Vedatori/Time-O-Mat/Mechanics/Box/Box - Front.stl

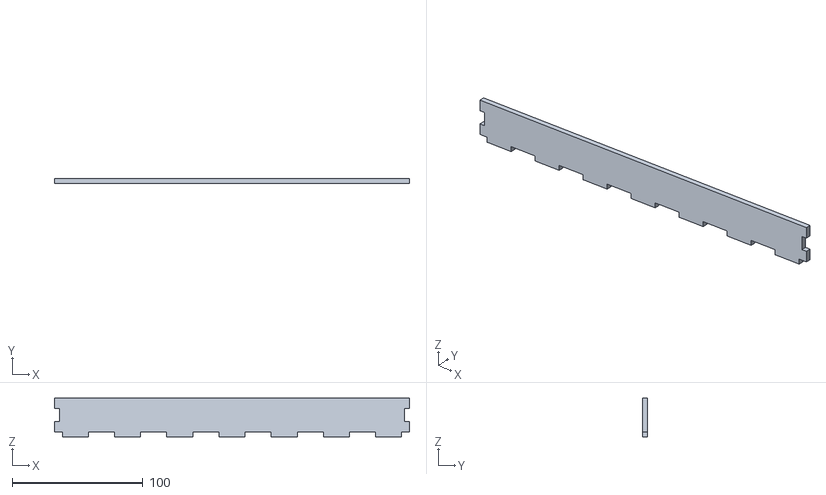
[picture p195: CAD file, 2022-08-20]
Mechanics/Box/Box - Front.stl
272.0 x 3.80 x 29.8
