Vedatori/Time-O-Mat/Mechanics/Eight/Eight v3 - Dot 3DP.stl

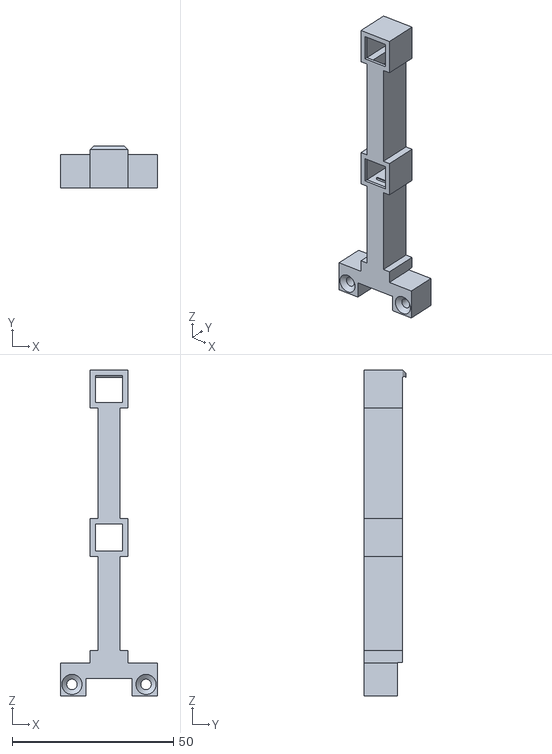
[picture p196: CAD file, 2022-08-20]
Mechanics/Eight/Eight v3 - Dot 3DP.stl
30.0 x 13.0 x 101.2
