Vedatori/Time-O-Mat/Mechanics/Eight/Eight v3 - Diffuser.stl

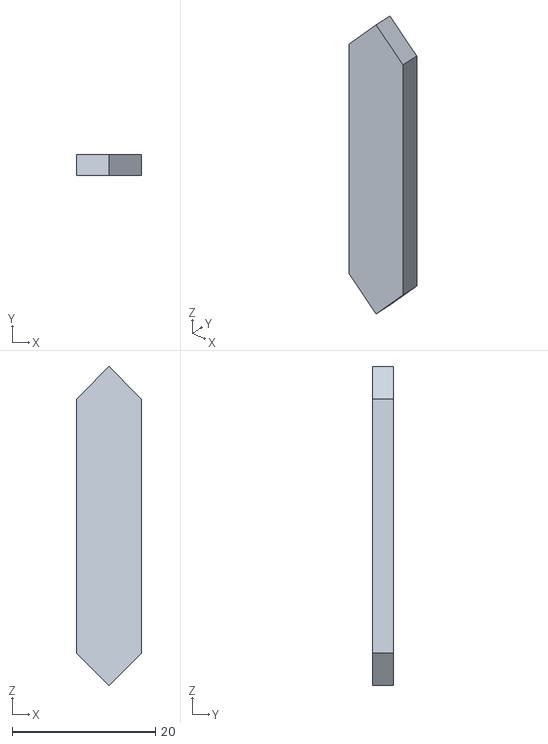
[picture p197: CAD file, 2022-08-20]
Mechanics/Eight/Eight v3 - Diffuser.stl
9.10 x 3.00 x 44.6
