Vedatori/Time-O-Mat/Mechanics/Box/Box - Stand 3DP.stl

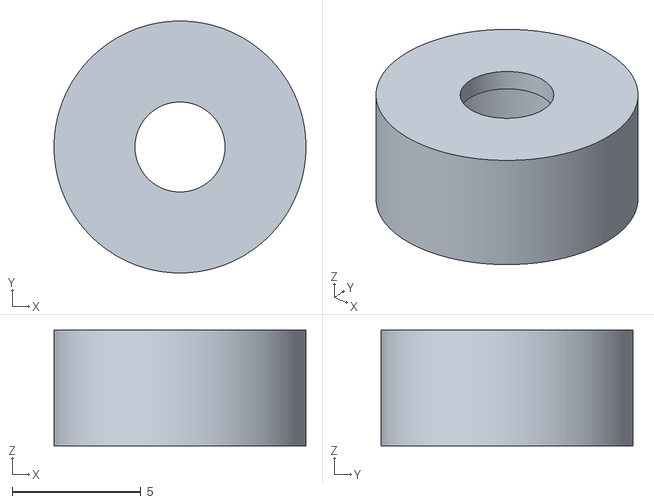
[picture p198: CAD file, 2022-08-20]
Mechanics/Box/Box - Stand 3DP.stl
9.80 x 9.80 x 4.50
