Vedatori/Time-O-Mat/Mechanics/Eight/Eight v3 - Dot spacer 3DP.stl

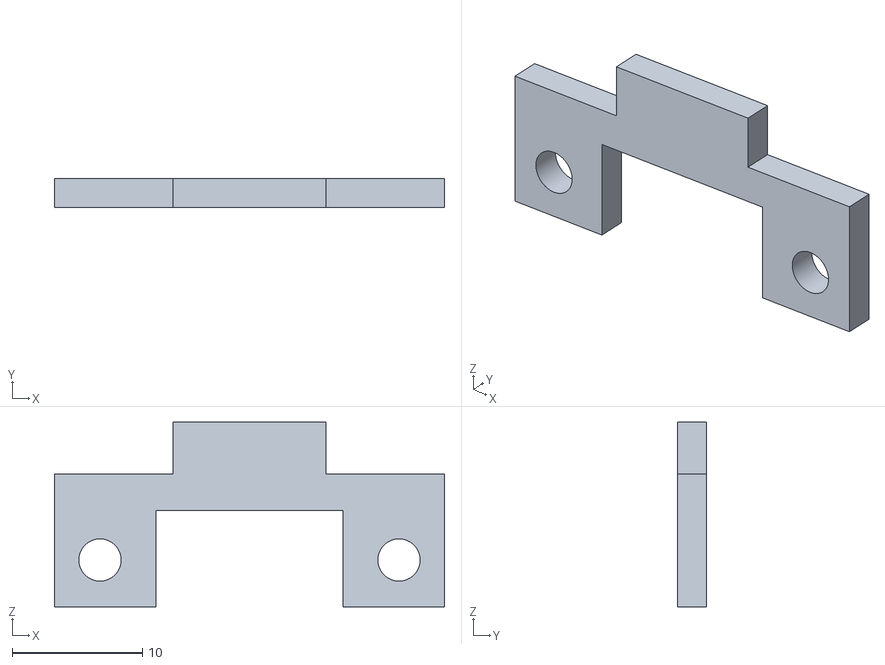
[picture p199: CAD file, 2022-08-20]
Mechanics/Eight/Eight v3 - Dot spacer 3DP.stl
30.0 x 2.25 x 14.2
