Vedatori/Time-O-Mat/Mechanics/Box/Box - Holder pt2 3DP.stl

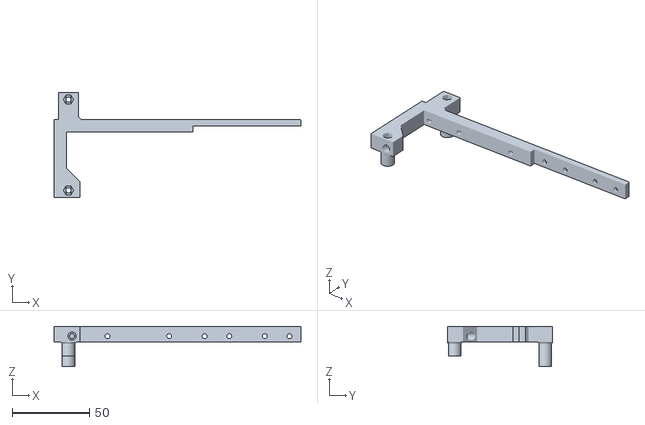
[picture p200: CAD file, 2022-08-20]
Mechanics/Box/Box - Holder pt2 3DP.stl
160.2 x 68.0 x 26.0
