Vedatori/Time-O-Mat/Mechanics/Box/box.dxf

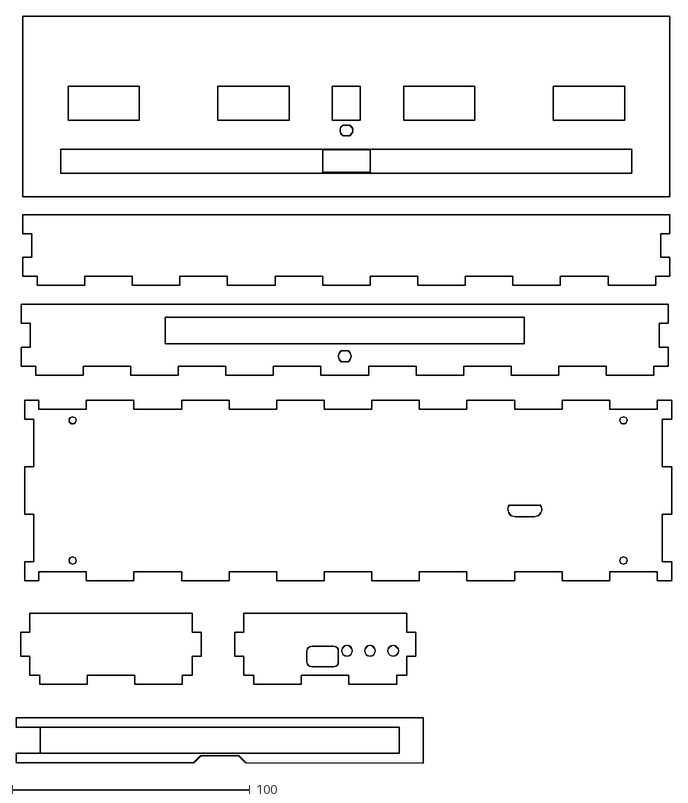
[picture p201: CAD file, 2022-08-20]
Mechanics/Box/box.dxf
275.4 x 314.1
