Vedatori/Time-O-Mat/Mechanics/Box/Box - Right.stl

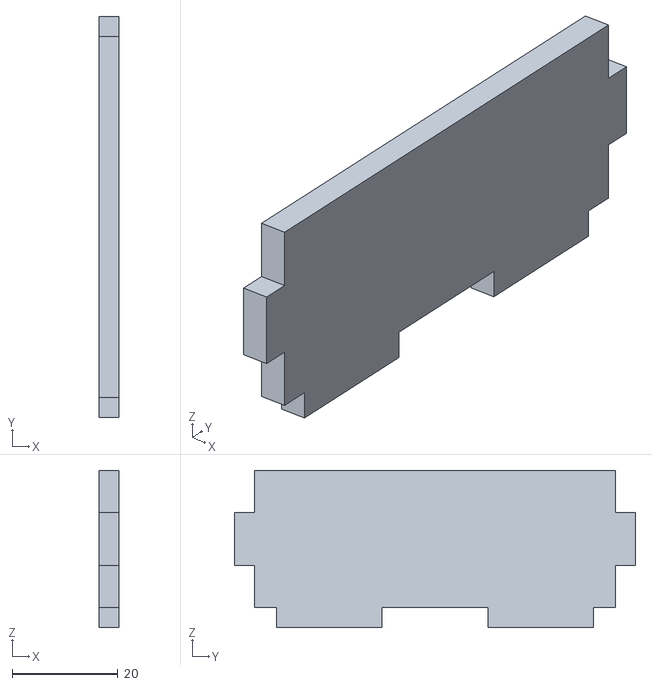
[picture p202: CAD file, 2022-08-20]
Mechanics/Box/Box - Right.stl
3.80 x 76.0 x 29.8
