Vedatori/Time-O-Mat/Mechanics/Box/Box - Holder pt1 3DP.stl

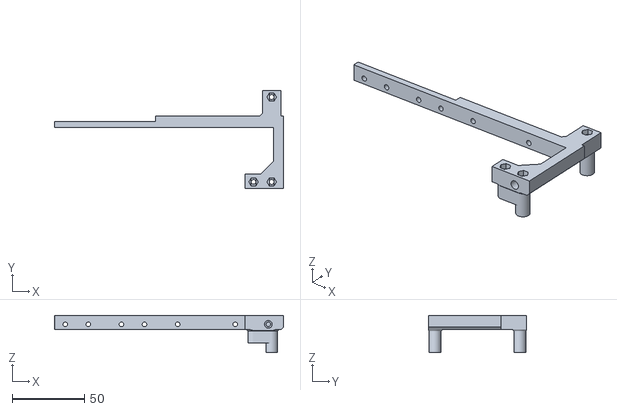
[picture p203: CAD file, 2022-08-20]
Mechanics/Box/Box - Holder pt1 3DP.stl
159.0 x 68.0 x 26.0
