Vedatori/Time-O-Mat/Mechanics/Box/Box - LED strip bracket.stl

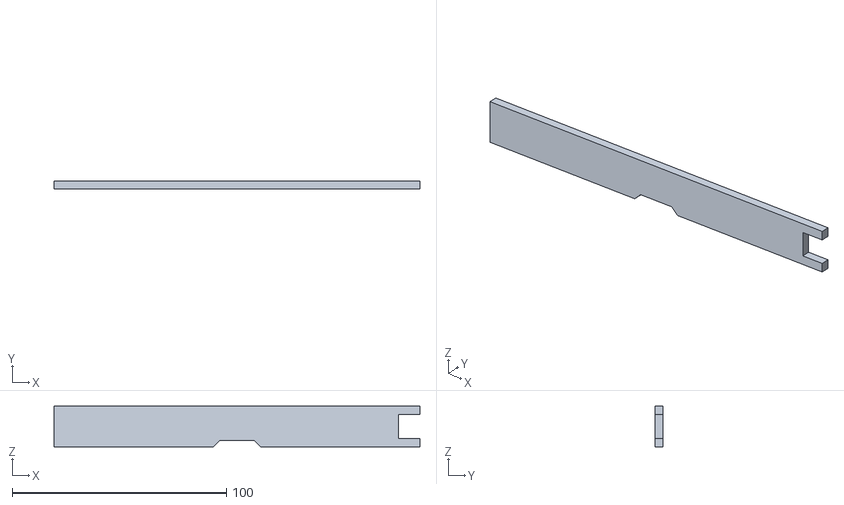
[picture p204: CAD file, 2022-08-20]
Mechanics/Box/Box - LED strip bracket.stl
171.0 x 3.80 x 19.0
