Vedatori/Time-O-Mat/Manuals/SupportFiles/IMG_2151.jpg

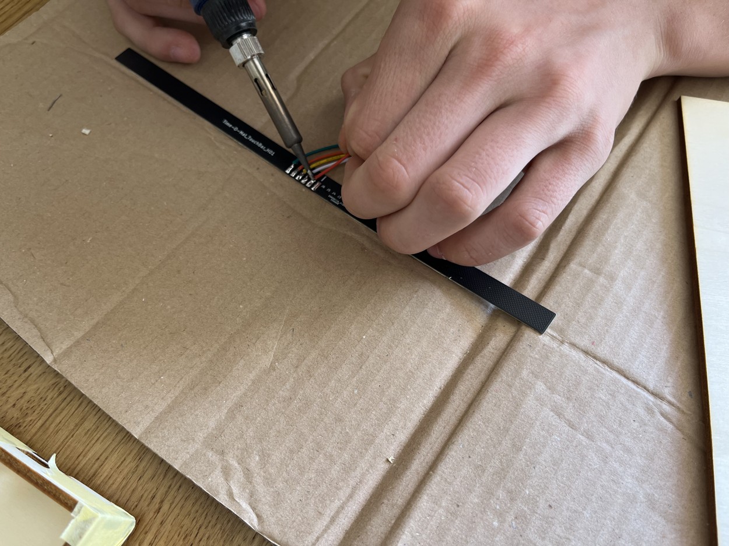
Manuals/SupportFiles/IMG_2151.jpg
