Vedatori/Time-O-Mat/Manuals/SupportFiles/IMG_3162.jpeg

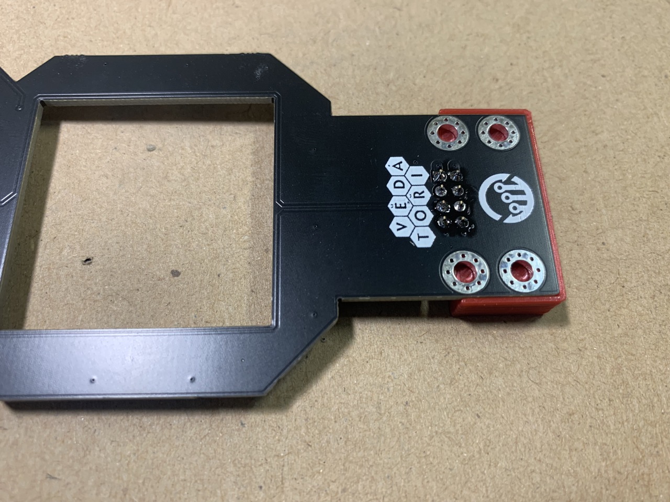
Manuals/SupportFiles/IMG_3162.jpeg
