Vedatori/Time-O-Mat/Manuals/SupportFiles/IMG_3452.jpeg

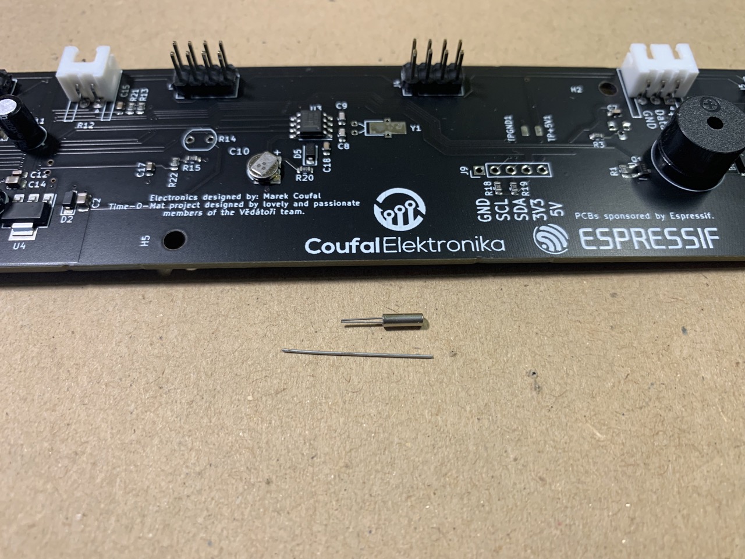
Manuals/SupportFiles/IMG_3452.jpeg
