Vedatori/Time-O-Mat/Manuals/SupportFiles/IMG_3628.jpeg

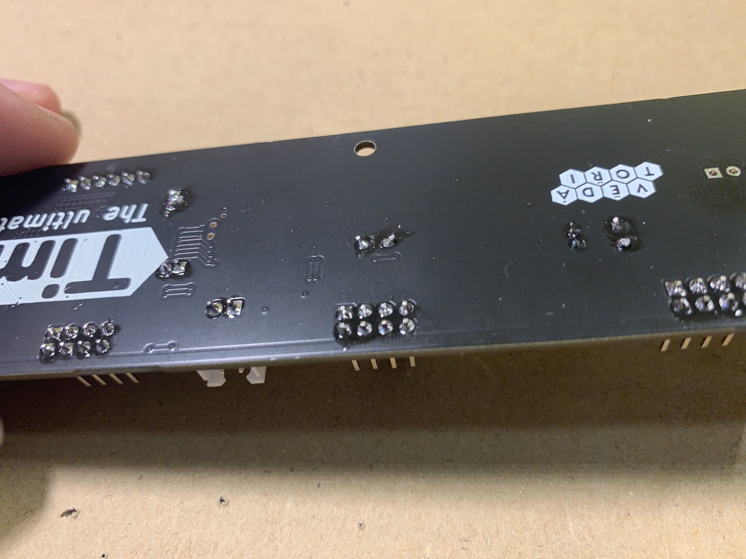
Manuals/SupportFiles/IMG_3628.jpeg
