Vedatori/Time-O-Mat/Manuals/SupportFiles/IMG_3641.jpeg

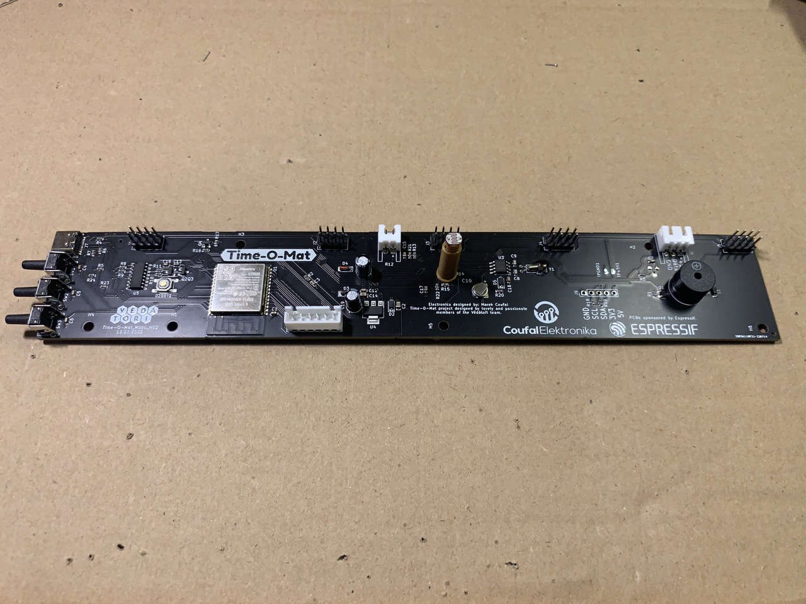
Manuals/SupportFiles/IMG_3641.jpeg
