Vedatori/Time-O-Mat/Manuals/SupportFiles/prog_web_root.png

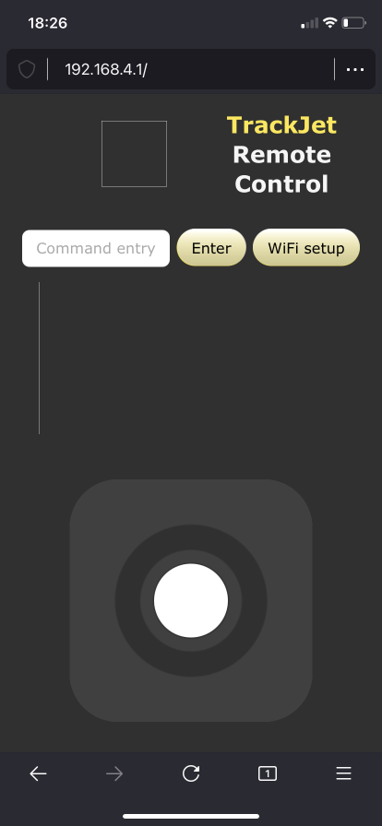
Manuals/SupportFiles/prog_web_root.png
